skot/Loriques/3d/CLV1A-FKB.stp

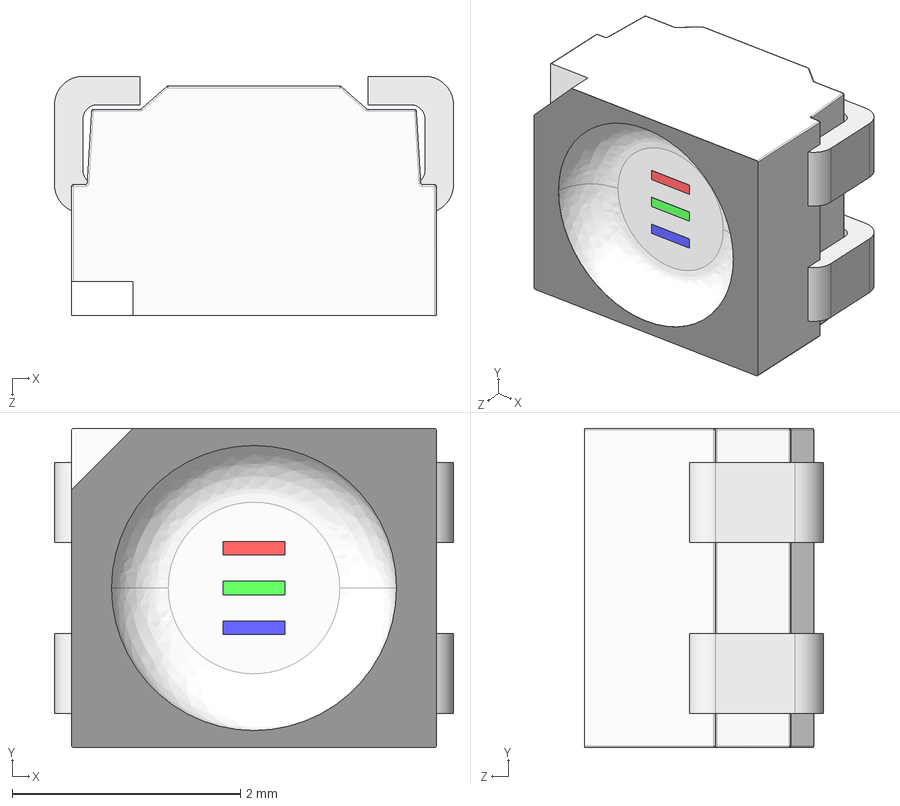
[picture p18: CAD file, 2025-07-11]
3d/CLV1A-FKB.stp
3.50 x 2.80 x 2.10 mm
terminal
top
red
green
blue
