skot/Loriques/3d/B3B-PH-SM4-TB.STEP

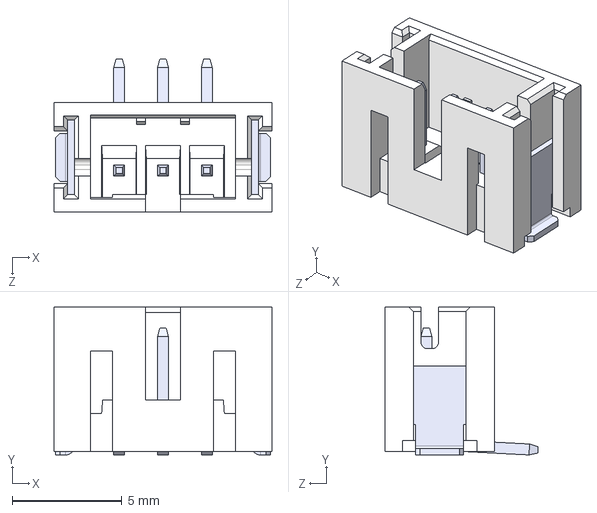
[picture p19: CAD file, 2025-07-11]
3d/B3B-PH-SM4-TB.STEP
9.95 x 6.75 x 7.00 mm
