skot/Loriques/3d/B4B-PH-SM4-TB.STEP

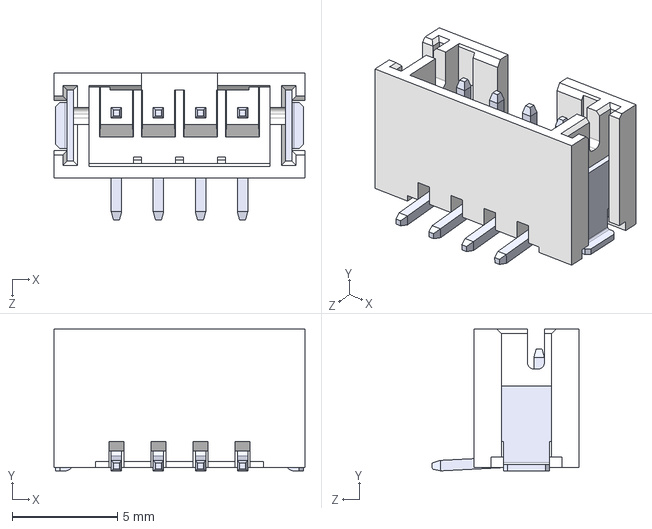
[picture p20: CAD file, 2025-07-11]
3d/B4B-PH-SM4-TB.STEP
12.0 x 6.75 x 7.00 mm
