skot/Loriques/3d/E22-900M30S.STEP

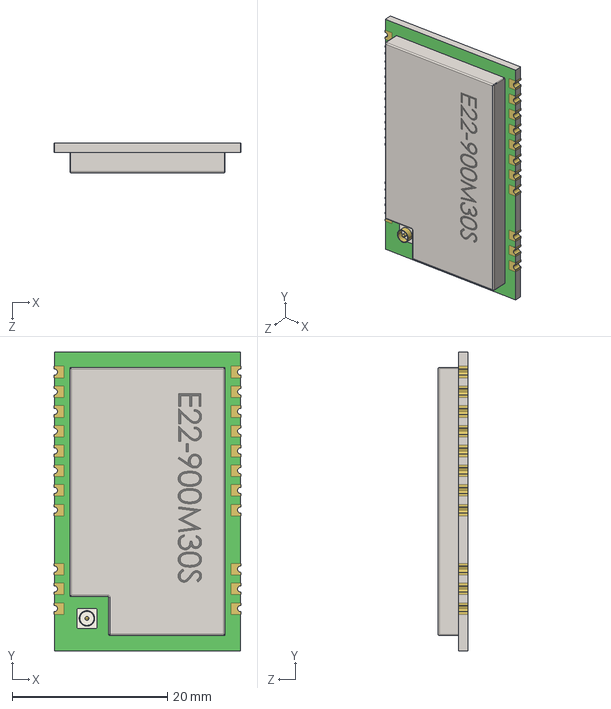
[picture p21: CAD file, 2025-07-11]
3d/E22-900M30S.STEP
24.0 x 38.5 x 3.88 mm
